Belan-Lab/TTL-trigger-timer/pic/image2.jpg

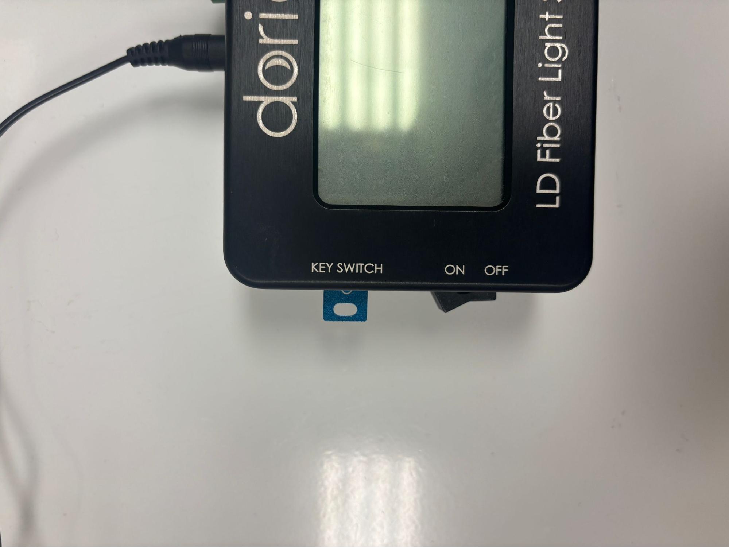
pic/image2.jpg
