Belan-Lab/TTL-trigger-timer/pic/image3.jpg

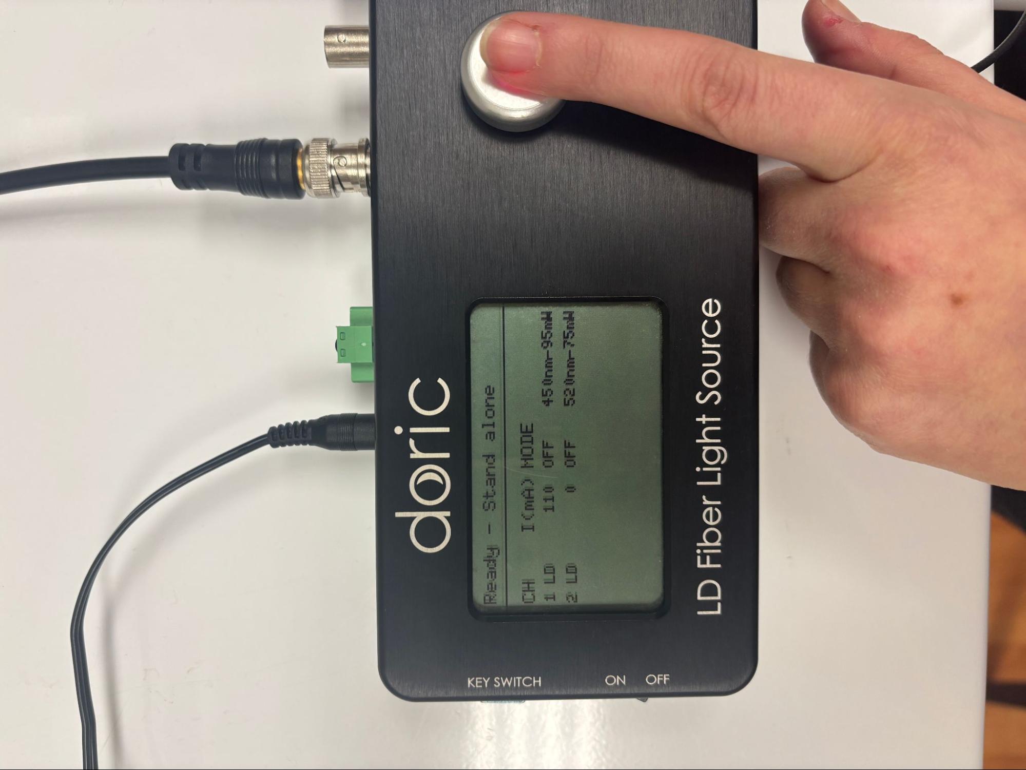
pic/image3.jpg
