Belan-Lab/TTL-trigger-timer/pic/image5.jpg

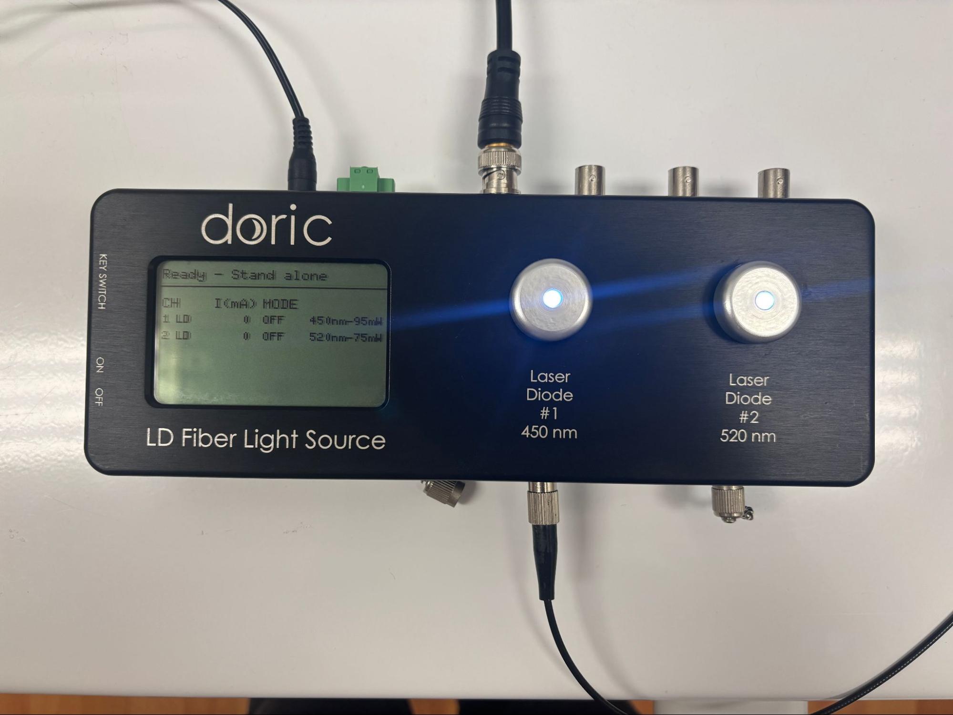
pic/image5.jpg
