Belan-Lab/TTL-trigger-timer/pic/image6.jpg

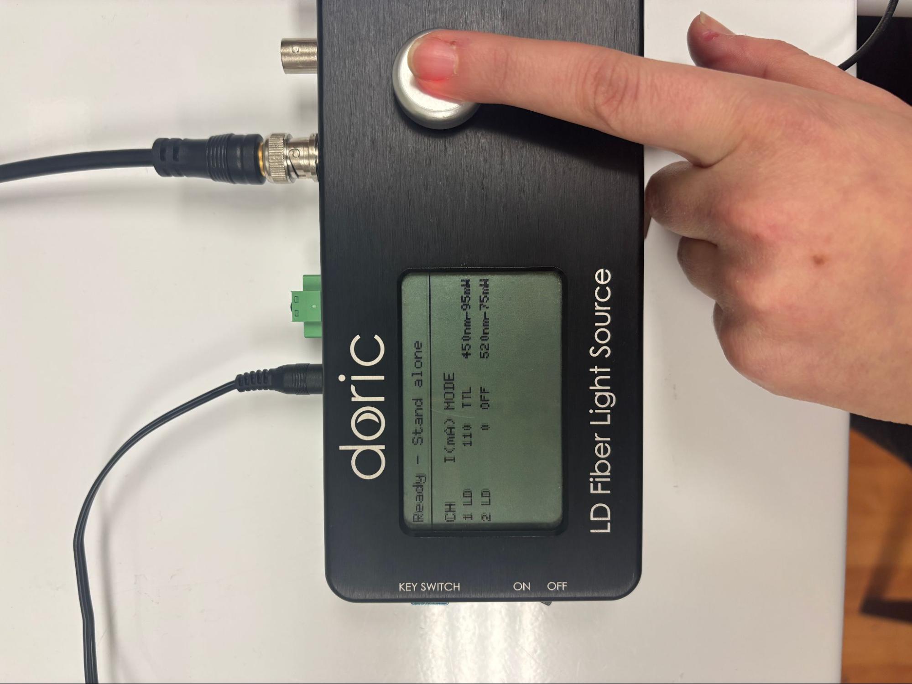
pic/image6.jpg
