Belan-Lab/TTL-trigger-timer/pic/image7.jpg

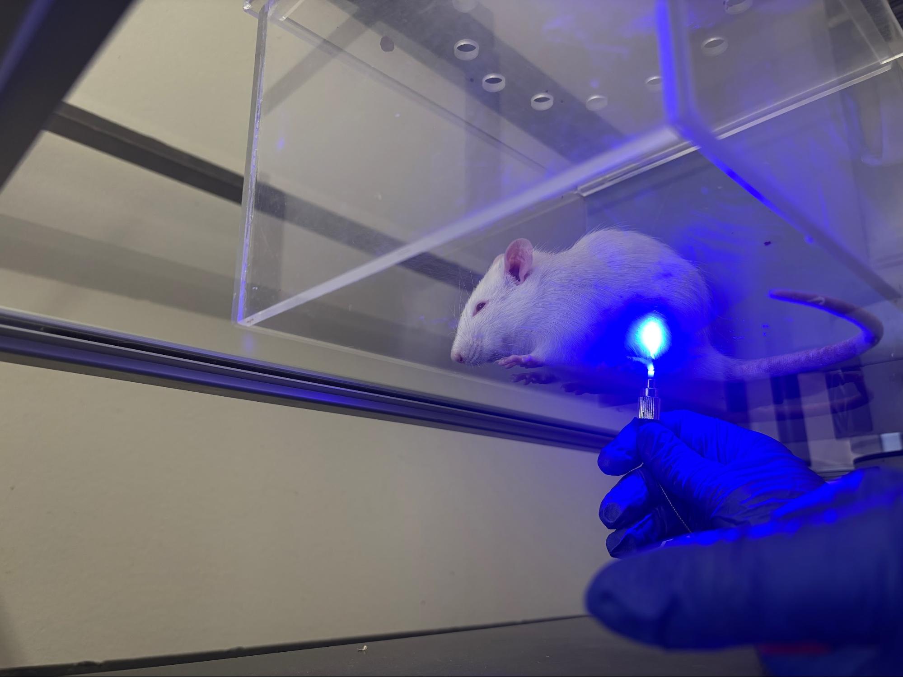
pic/image7.jpg
