Belan-Lab/TTL-trigger-timer/pic/image8.jpg

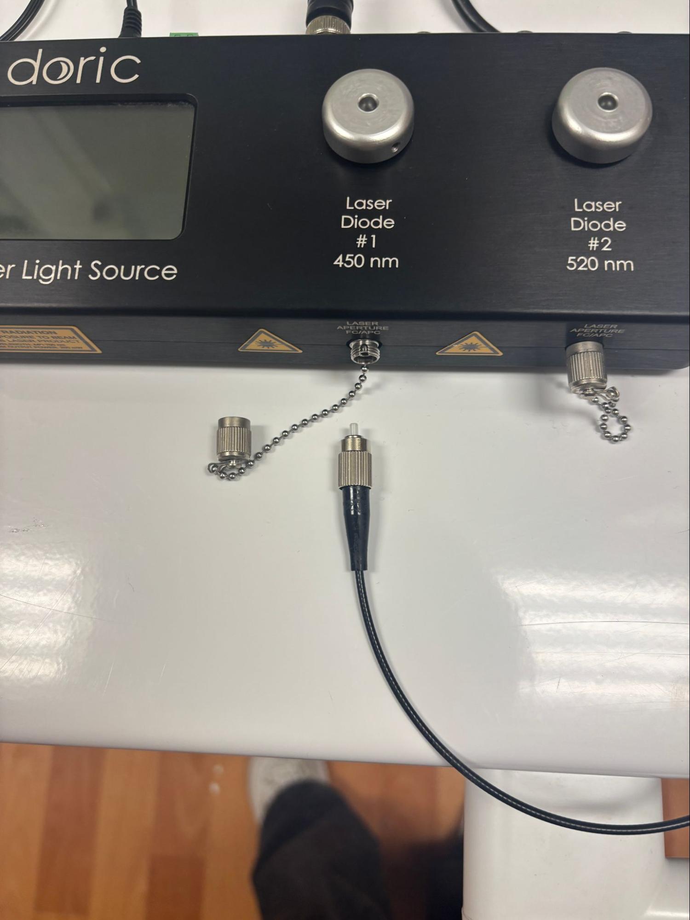
pic/image8.jpg
