Belan-Lab/TTL-trigger-timer/pic/image9.jpg

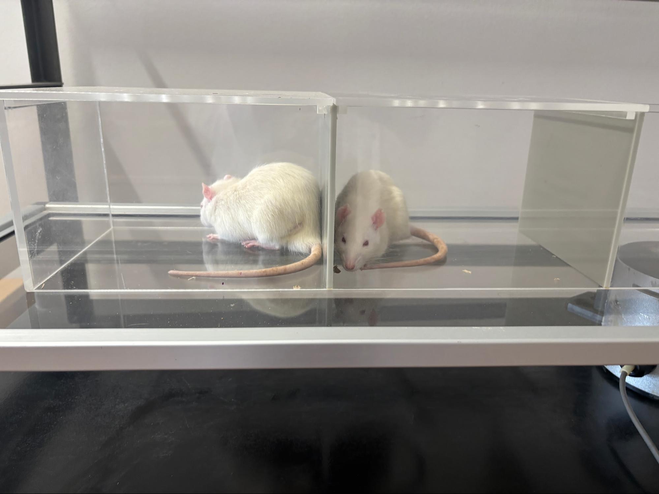
pic/image9.jpg
