Belan-Lab/TTL-trigger-timer/pic/image10.jpg

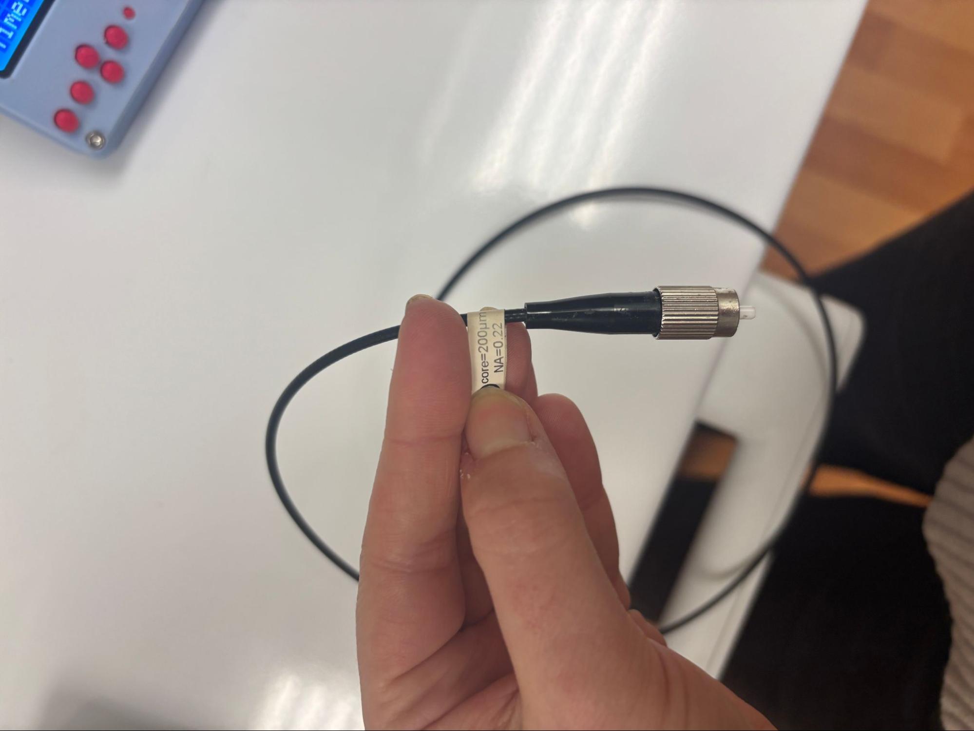
pic/image10.jpg
