Belan-Lab/TTL-trigger-timer/pic/image11.jpg

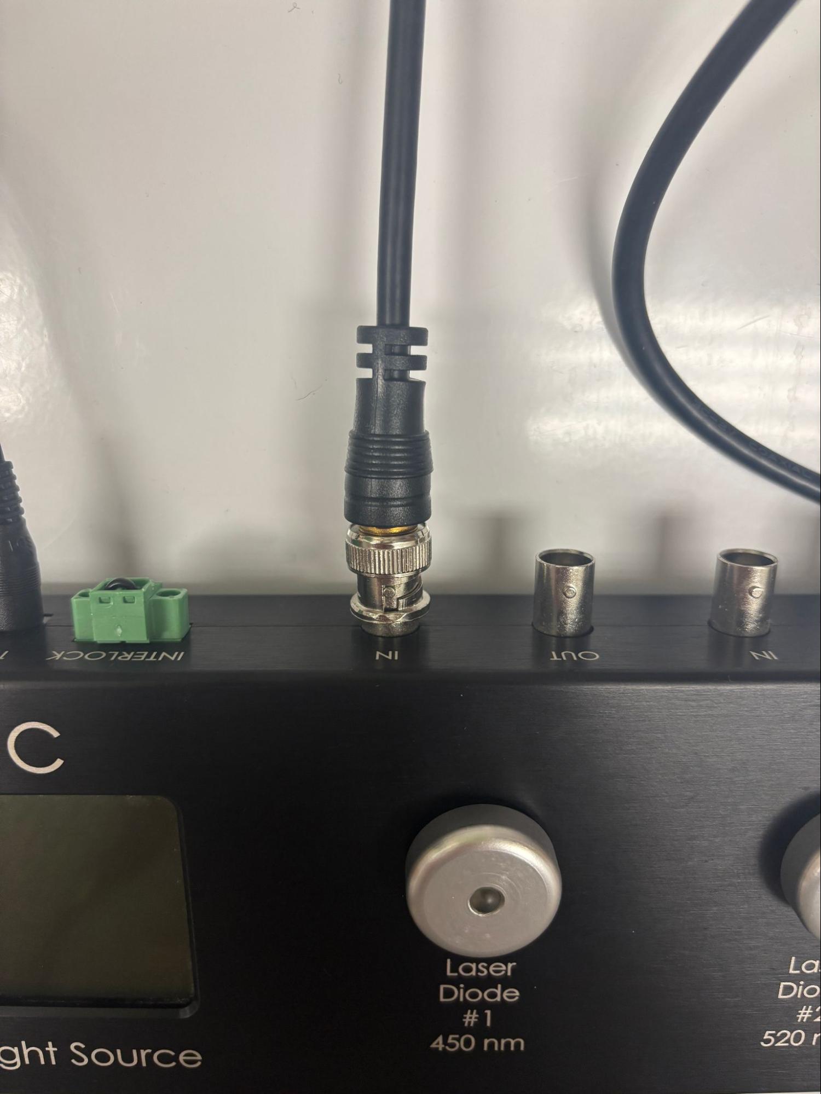
pic/image11.jpg
