Belan-Lab/TTL-trigger-timer/pic/image13.jpg

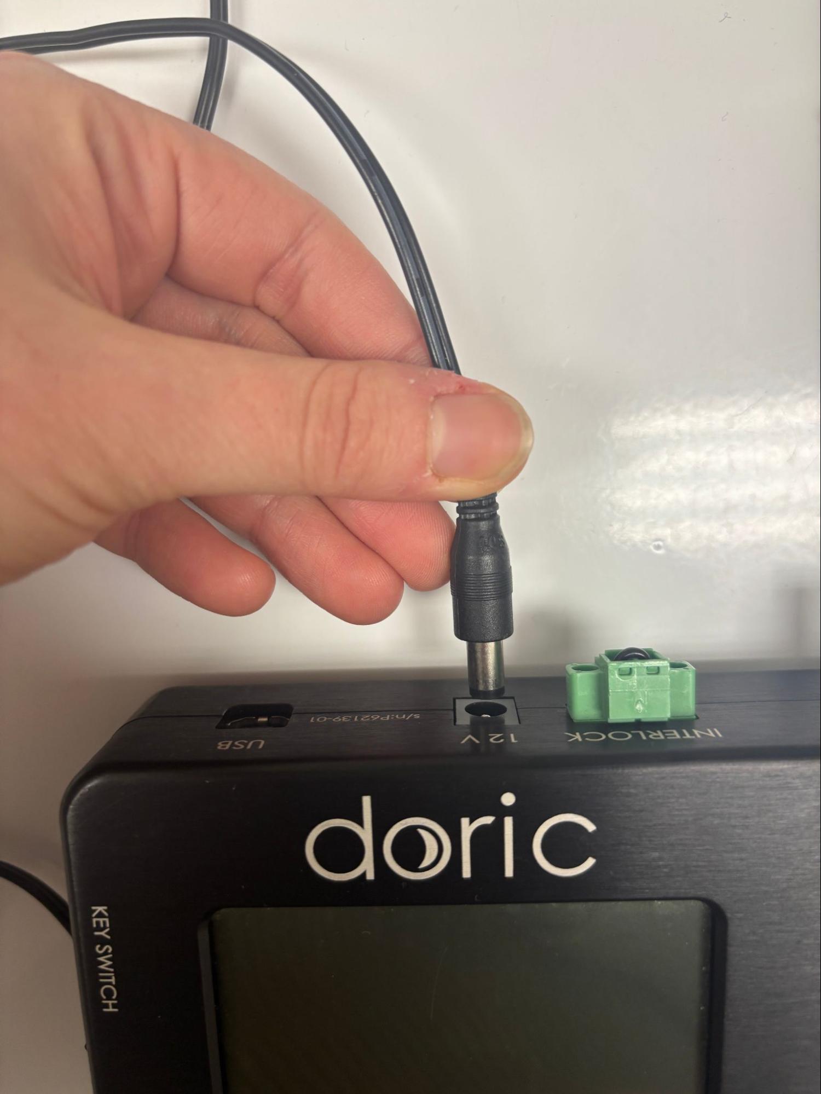
pic/image13.jpg
