Belan-Lab/TTL-trigger-timer/pic/image15.jpg

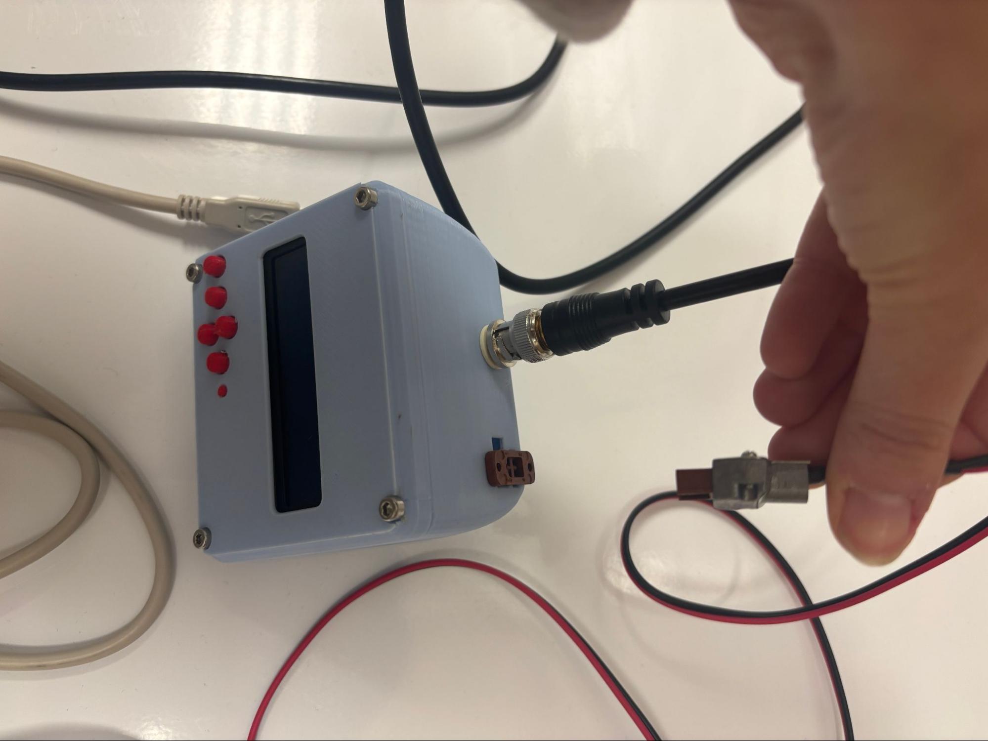
pic/image15.jpg
