Belan-Lab/TTL-trigger-timer/pic/image17.jpg

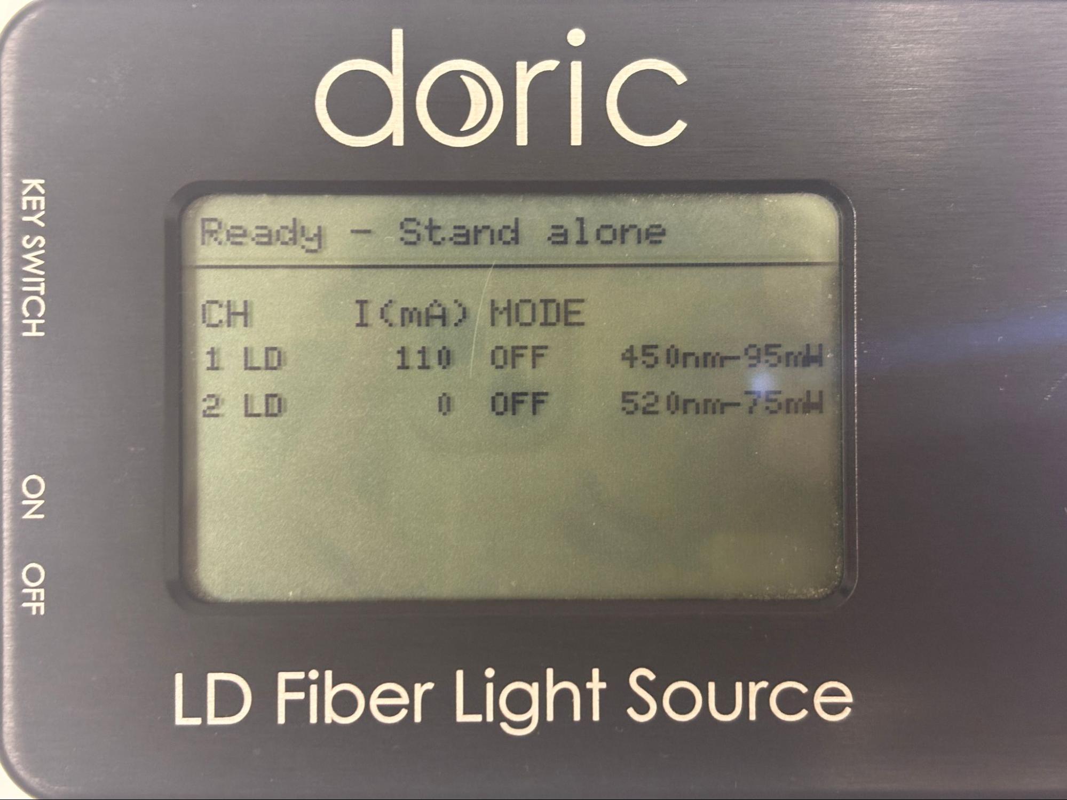
pic/image17.jpg
