Belan-Lab/TTL-trigger-timer/pic/image18.jpg

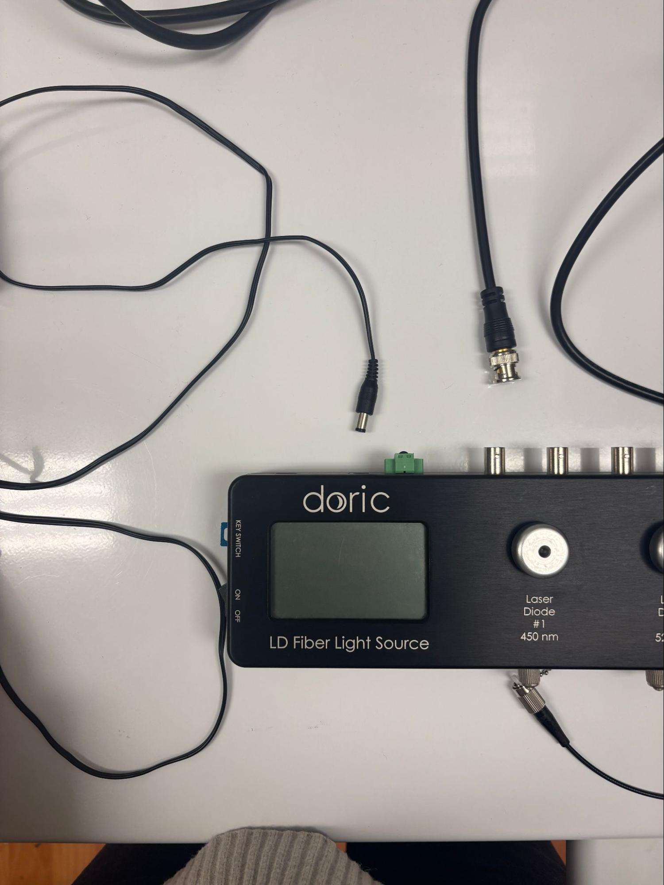
pic/image18.jpg
