Belan-Lab/TTL-trigger-timer/pic/image19.jpg

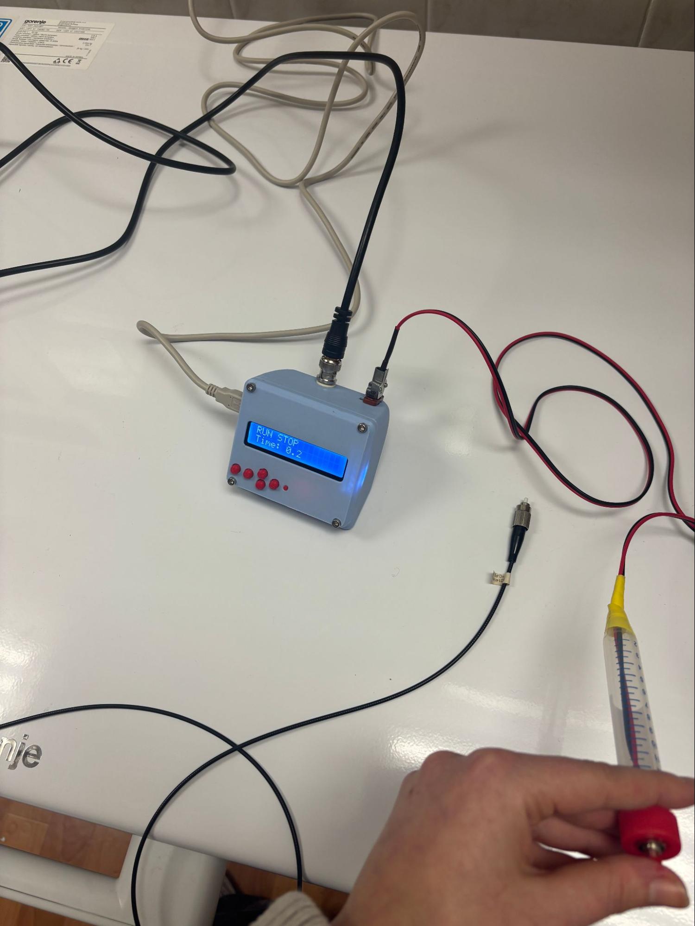
pic/image19.jpg
