Belan-Lab/TTL-trigger-timer/pic/image20.jpg

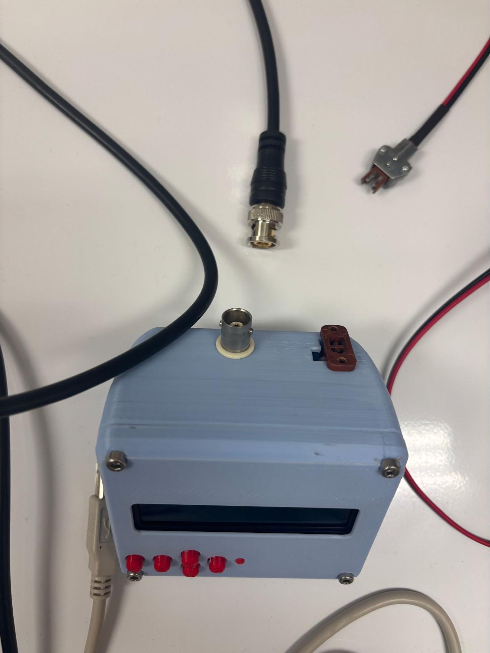
pic/image20.jpg
