Belan-Lab/TTL-trigger-timer/pic/image21.jpg

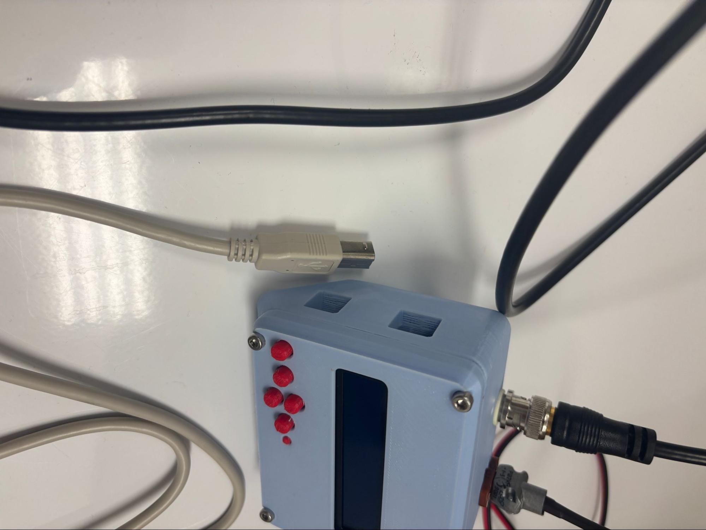
pic/image21.jpg
