Belan-Lab/TTL-trigger-timer/pic/image22.jpg

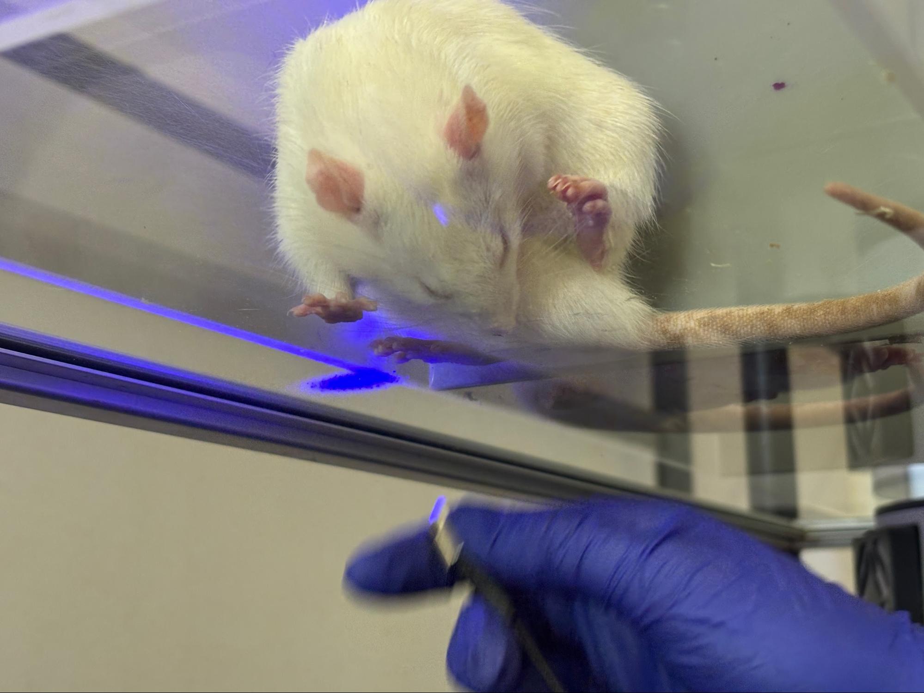
pic/image22.jpg
