Belan-Lab/TTL-trigger-timer/pic/image23.jpg

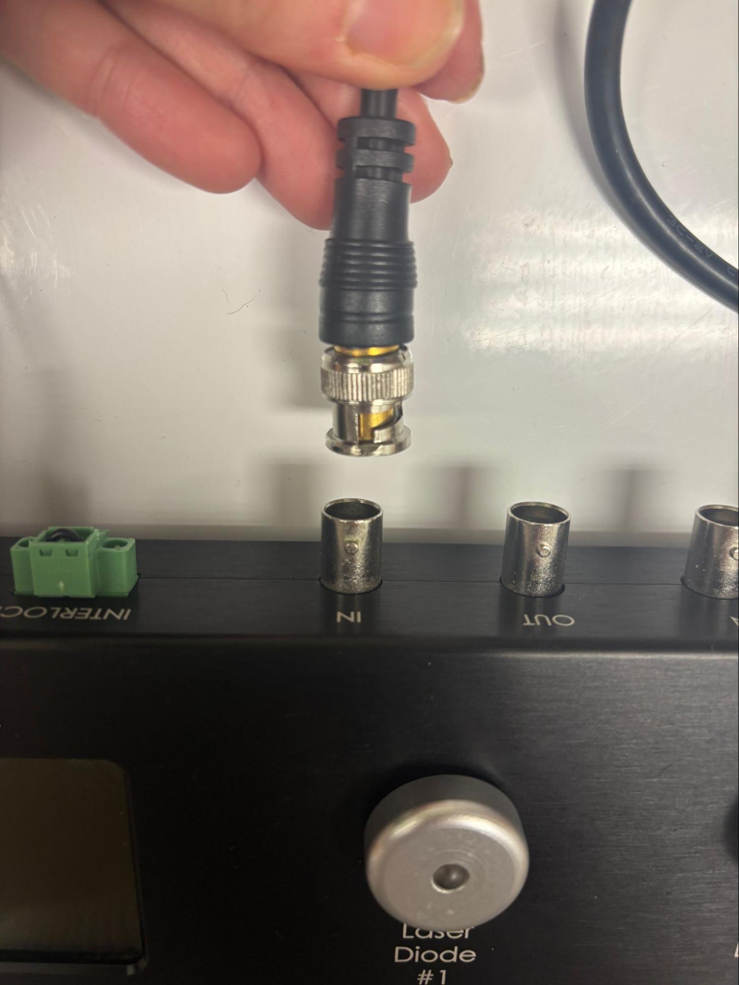
pic/image23.jpg
