Belan-Lab/TTL-trigger-timer/pic/image24.jpg

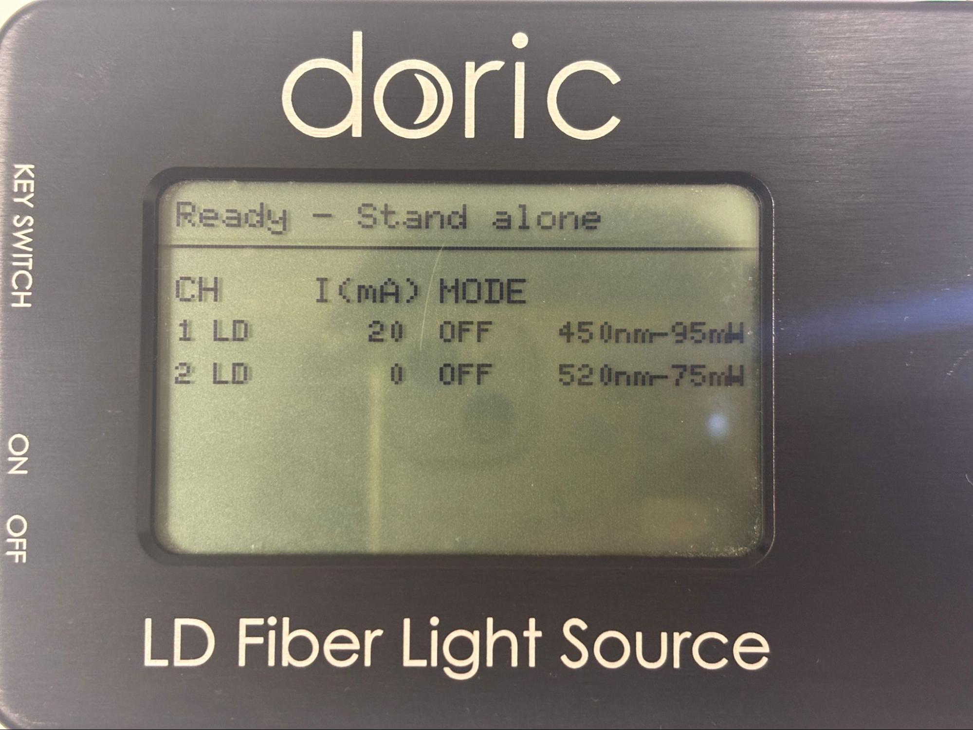
pic/image24.jpg
