Belan-Lab/TTL-trigger-timer/pic/image25.jpg

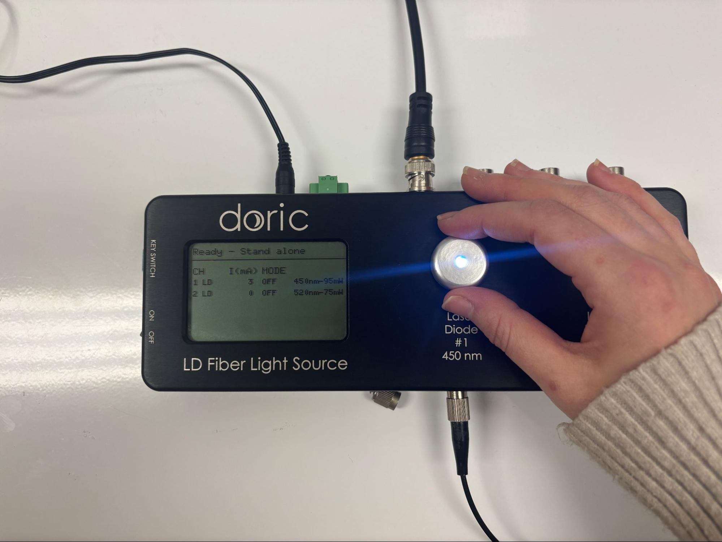
pic/image25.jpg
