Belan-Lab/TTL-trigger-timer/pic/image26.jpg

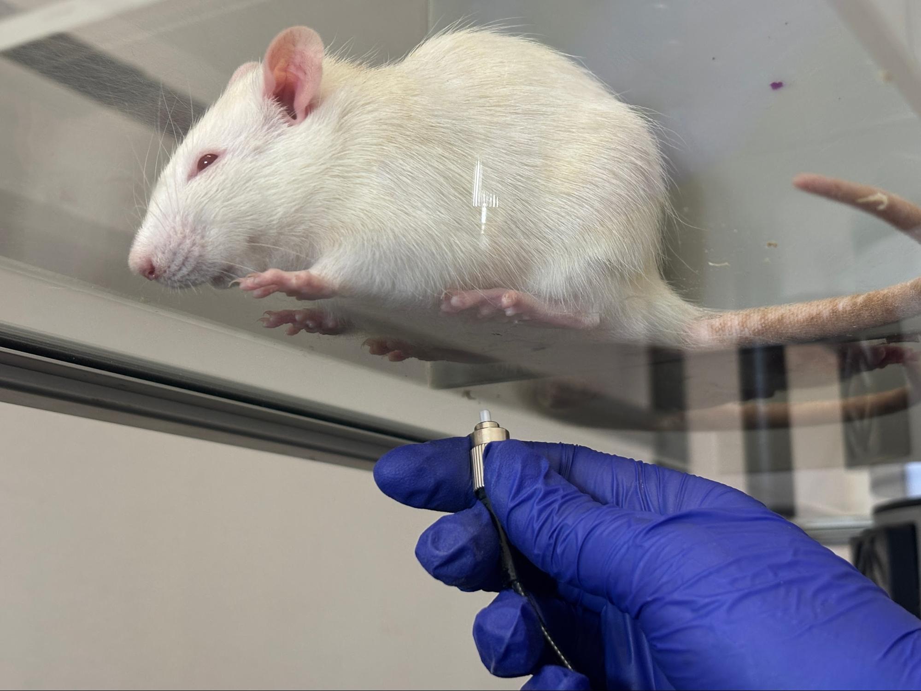
pic/image26.jpg
