Belan-Lab/TTL-trigger-timer/pic/image28.jpg

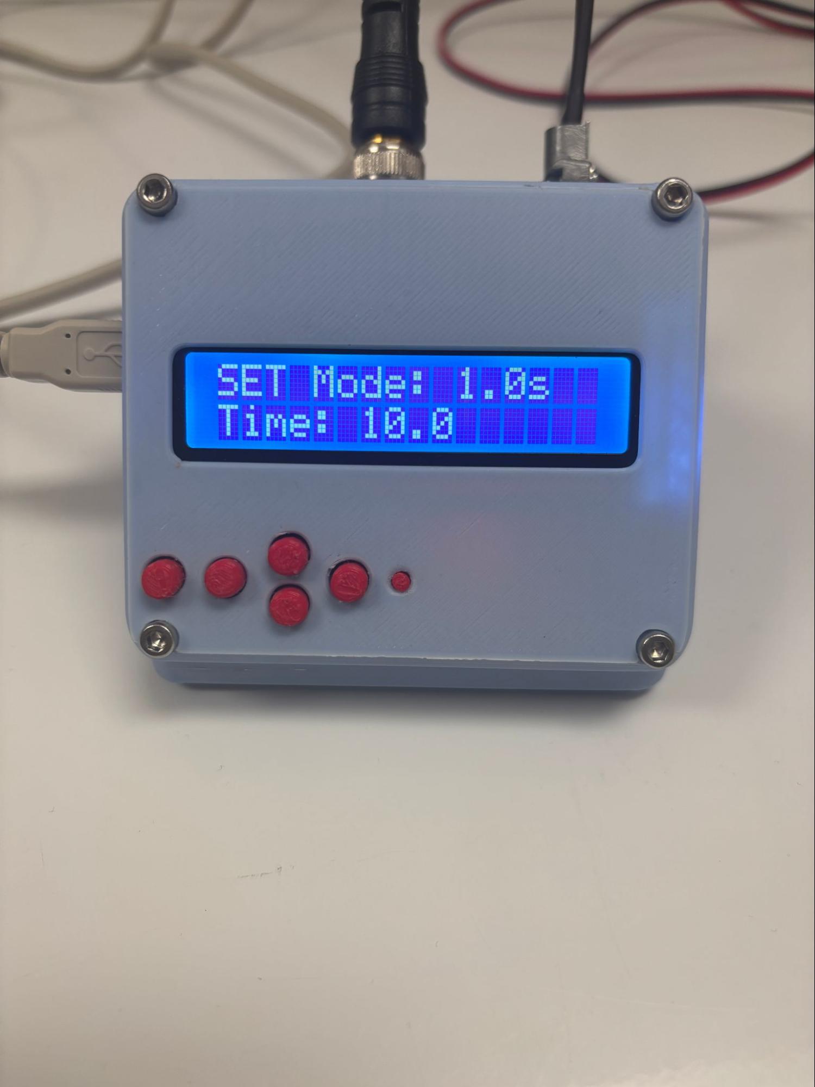
pic/image28.jpg
