Belan-Lab/TTL-trigger-timer/pic/image29.jpg

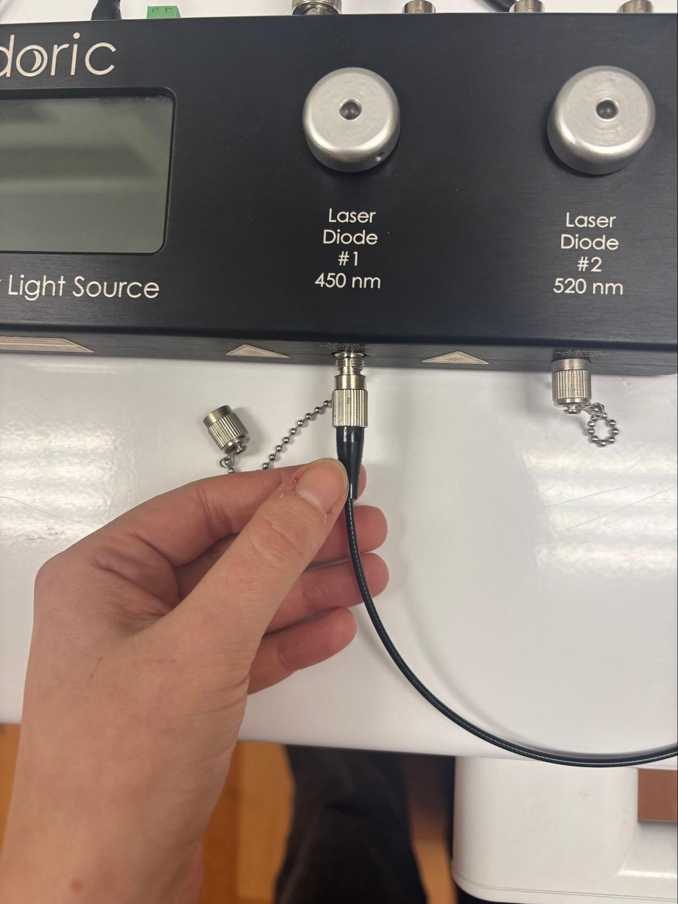
pic/image29.jpg
