Belan-Lab/TTL-trigger-timer/pic/image30.jpg

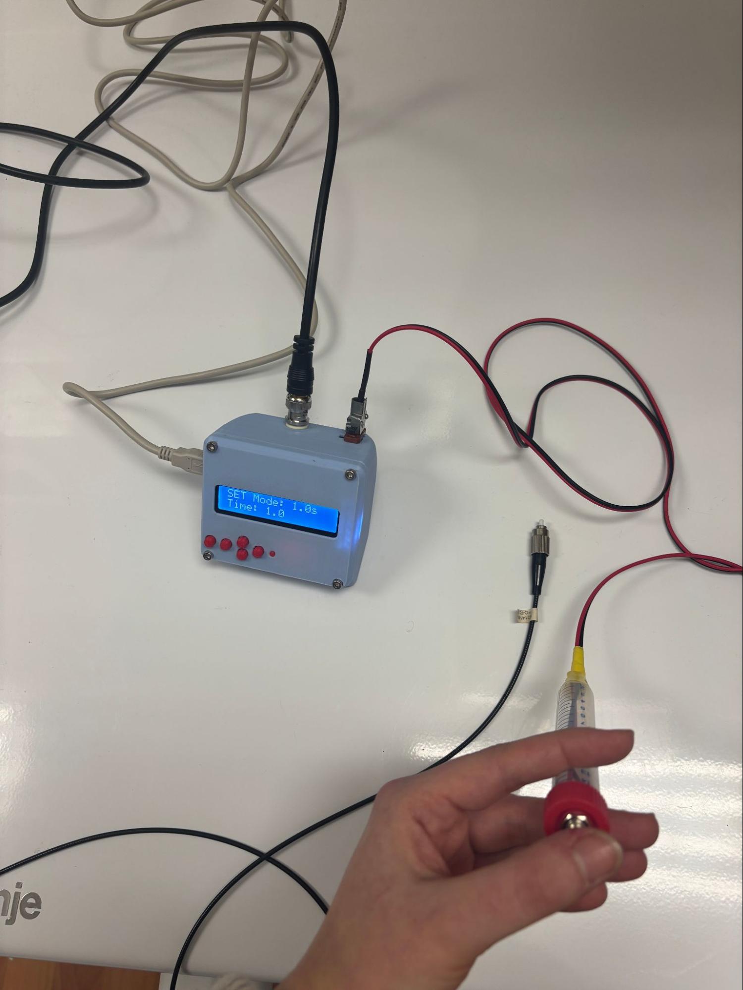
pic/image30.jpg
