Belan-Lab/TTL-trigger-timer/pic/image32.jpg

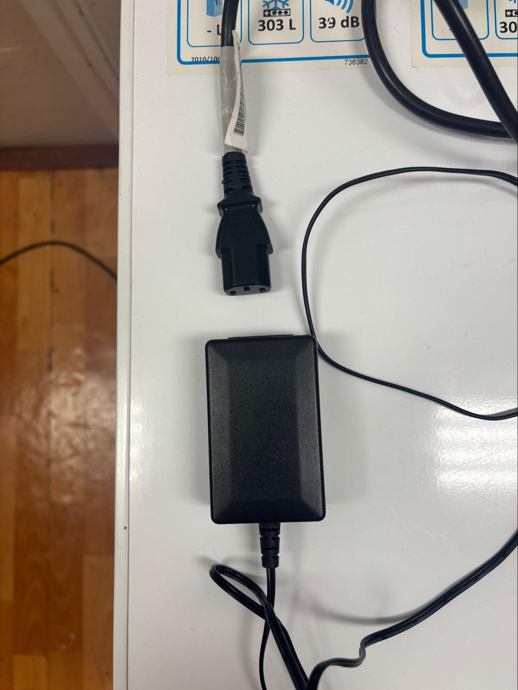
pic/image32.jpg
