Belan-Lab/TTL-trigger-timer/pic/image36.jpg

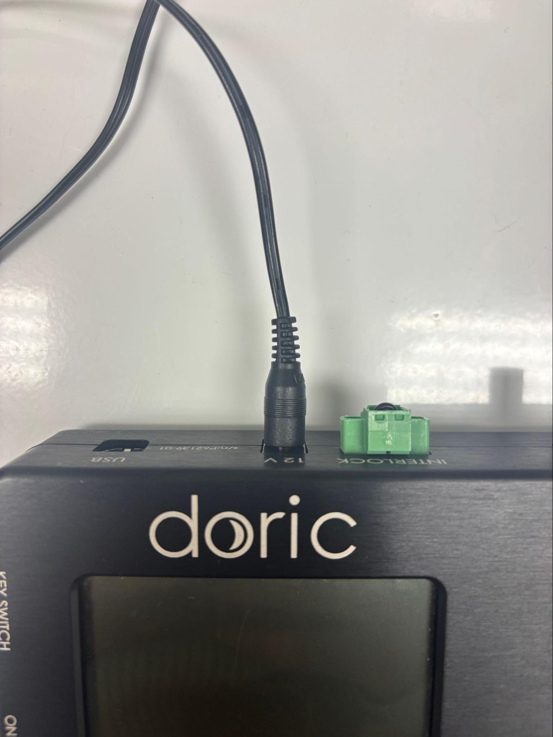
pic/image36.jpg
