Belan-Lab/TTL-trigger-timer/pic/image37.jpg

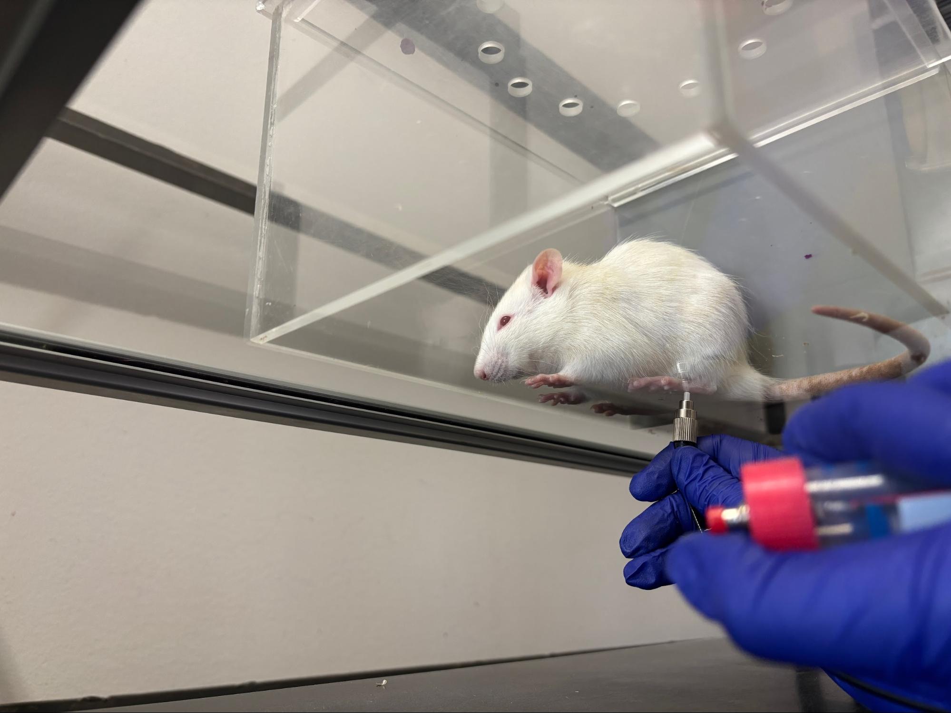
pic/image37.jpg
