Belan-Lab/TTL-trigger-timer/pic/image38.jpg

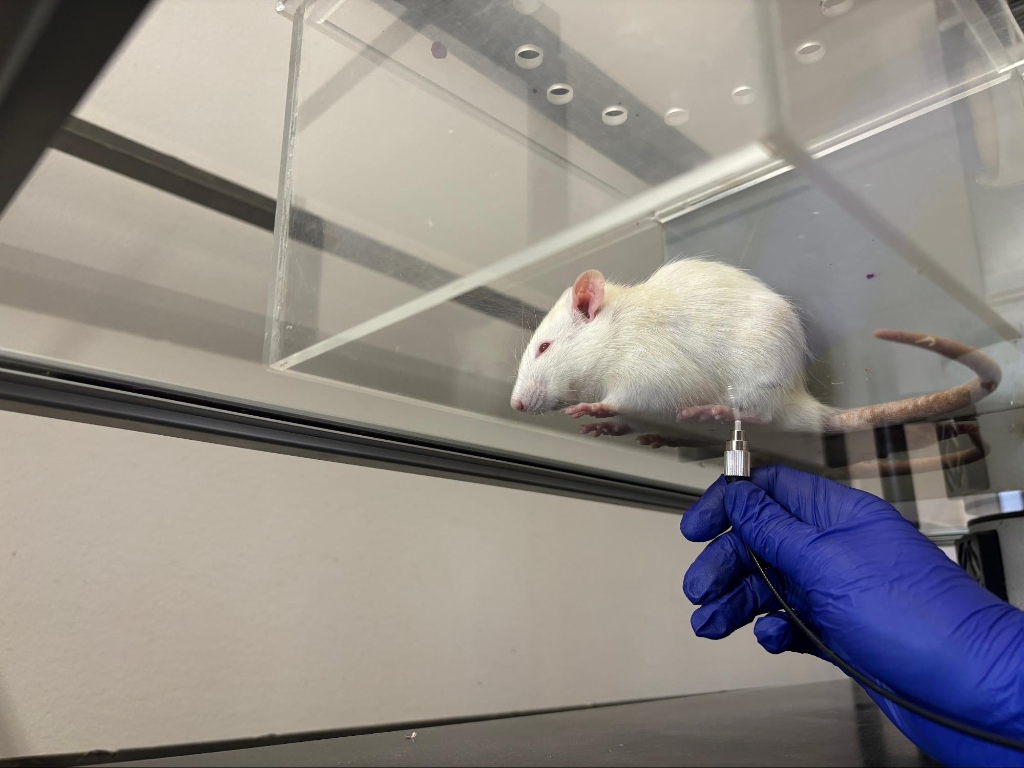
pic/image38.jpg
