Belan-Lab/TTL-trigger-timer/pic/image39.jpg

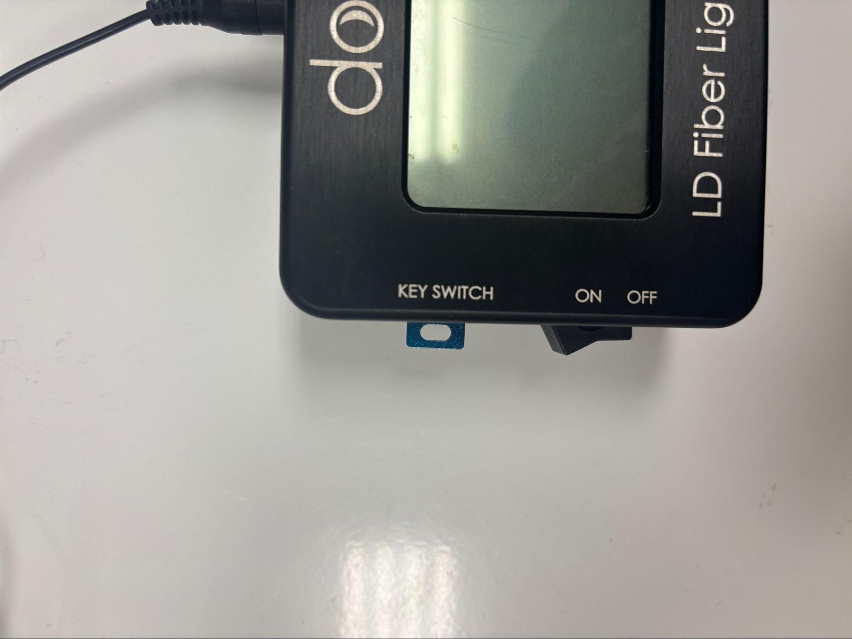
pic/image39.jpg
