Belan-Lab/TTL-trigger-timer/stl/v2/images/6247408b-b0bc-4db5-a6aa-e20a7e8e6d7e.png

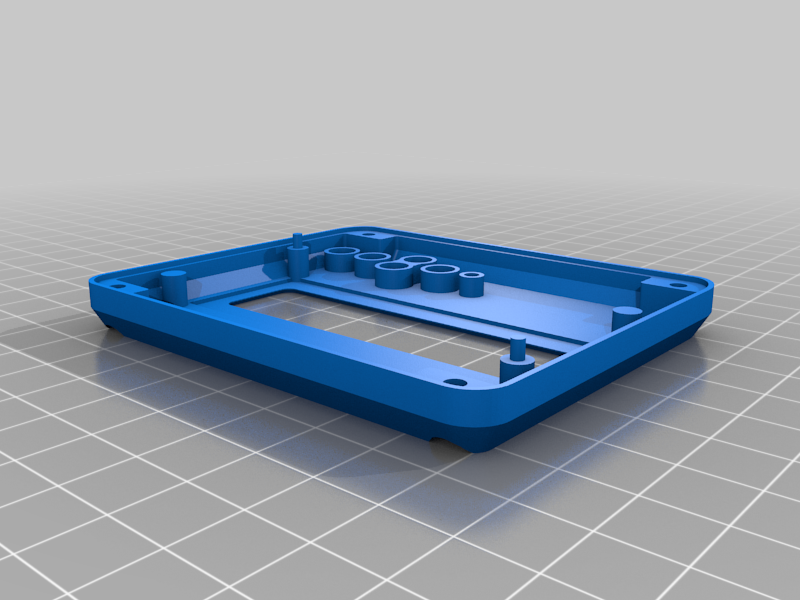
stl/v2/images/6247408b-b0bc-4db5-a6aa-e20a7e8e6d7e.png
