Belan-Lab/TTL-trigger-timer/stl/v2/images/case1.jpg

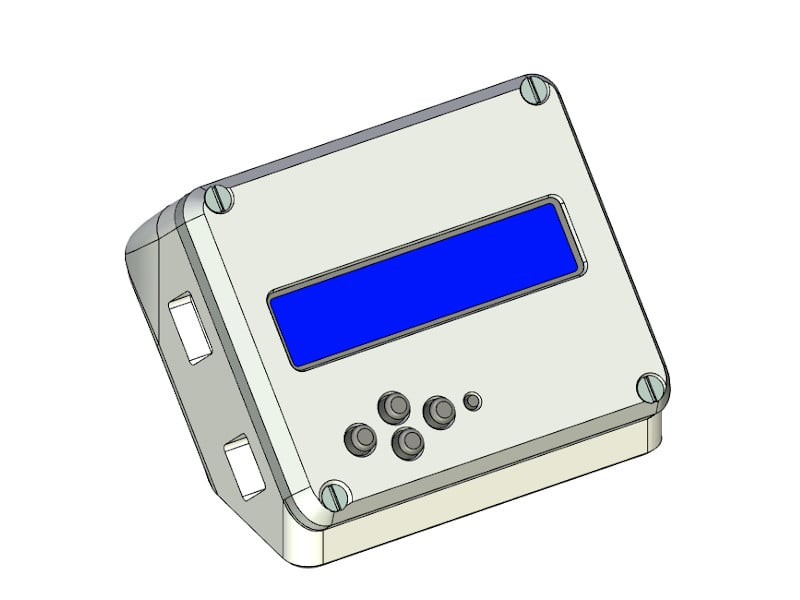
stl/v2/images/case1.jpg
