Belan-Lab/TTL-trigger-timer/stl/v2/images/case2.jpg

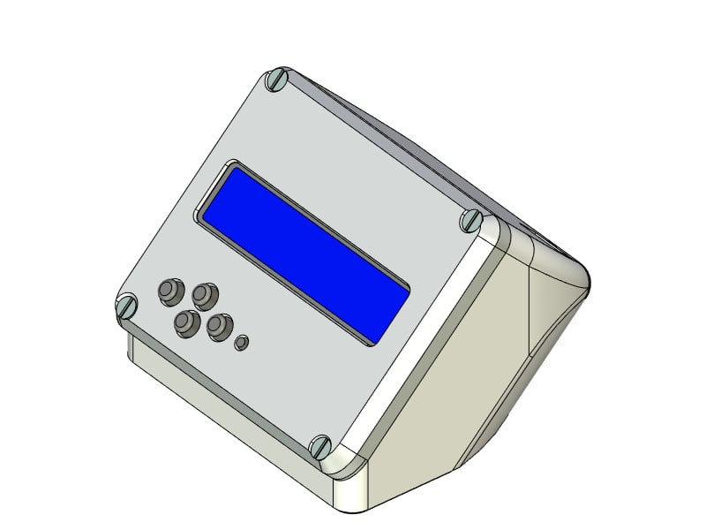
stl/v2/images/case2.jpg
