Belan-Lab/TTL-trigger-timer/stl/v2/images/f2b7d92e-70a1-48d4-b3af-a539b45f1684.png

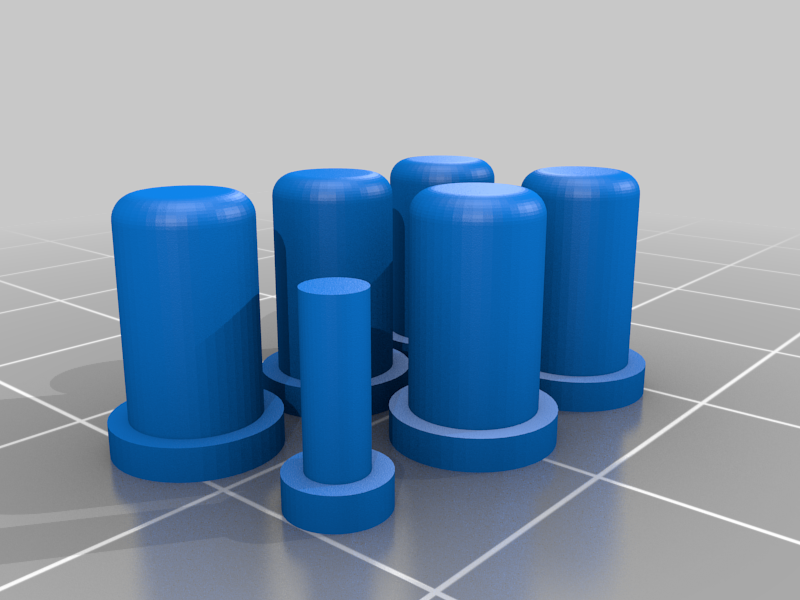
stl/v2/images/f2b7d92e-70a1-48d4-b3af-a539b45f1684.png
