Belan-Lab/TTL-trigger-timer/stl/v2/images/fig2.jpg

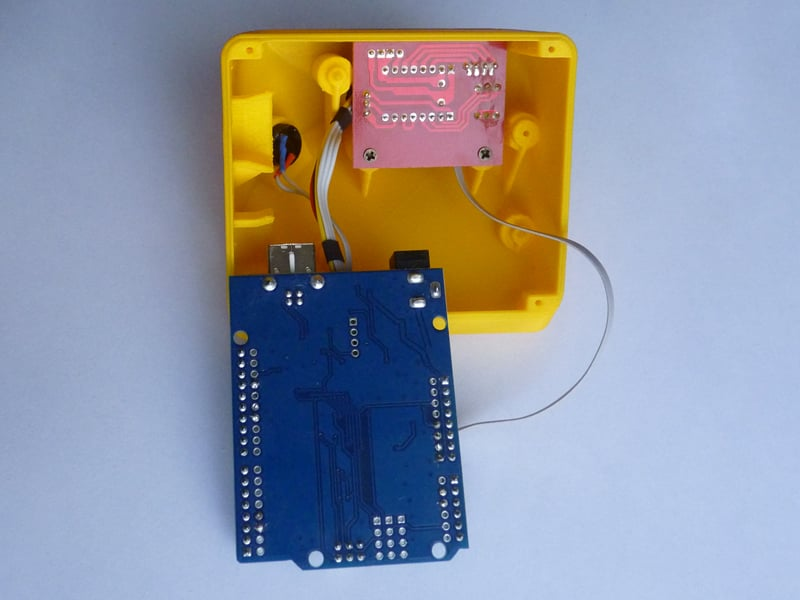
stl/v2/images/fig2.jpg
