Belan-Lab/TTL-trigger-timer/stl/v2/images/fig3.jpg

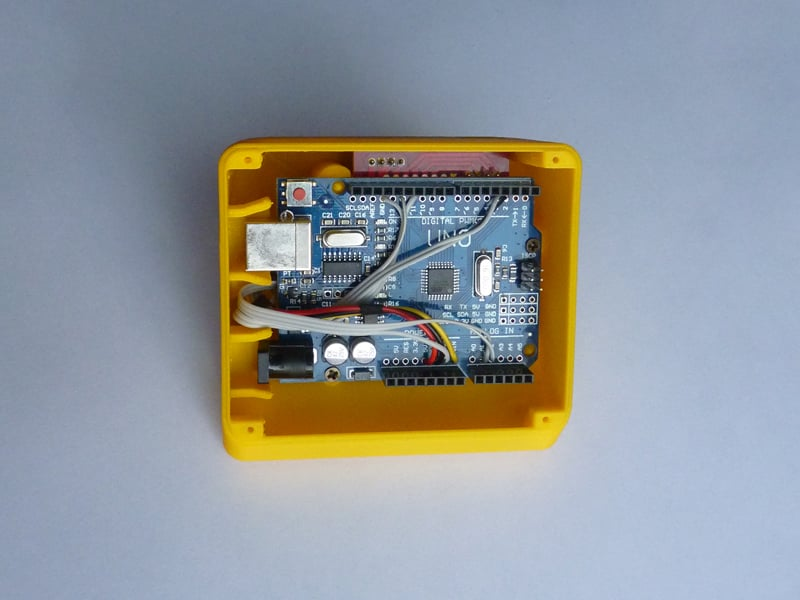
stl/v2/images/fig3.jpg
